gadjet/EP1-Alternative-Enclosure/Section Analysis_1.jpg

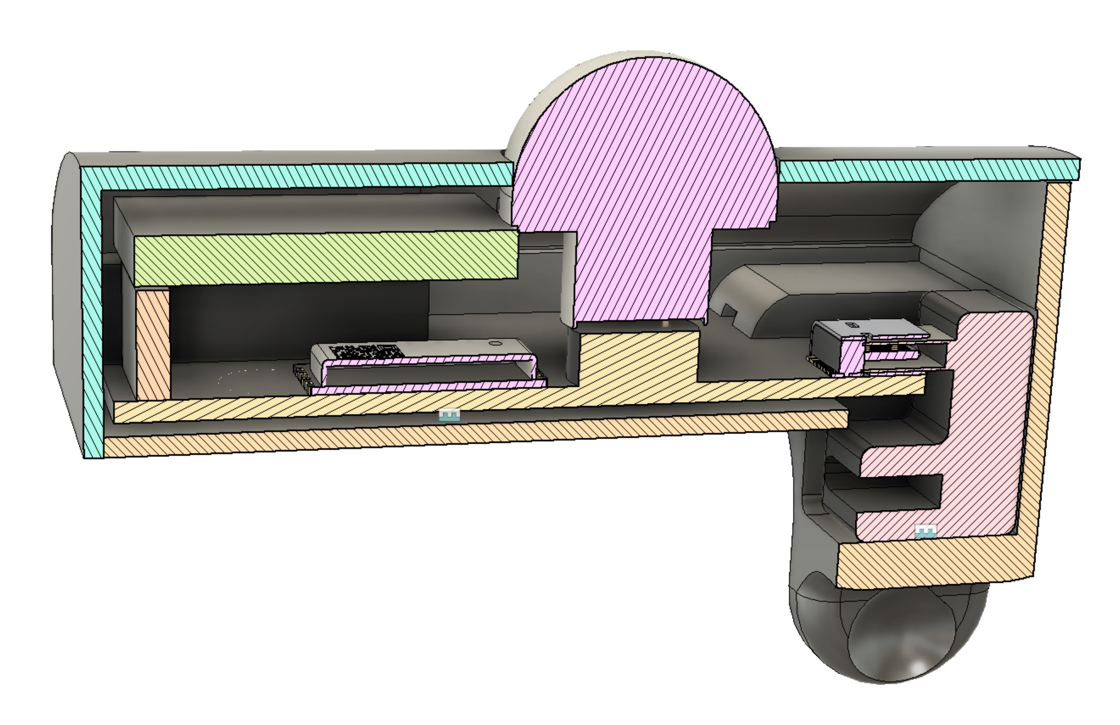
Section Analysis_1.jpg
